Artisfera/MP3-Gotchi-v2/hardware/MP3-Gotchi-v2_kicad/MP3-Gotchi-v2_kicad.kicad_sch

## KiCad design hardware/MP3-Gotchi-v2_kicad/MP3-Gotchi-v2_kicad.kicad_sch (2026-07-09, an earlier design)

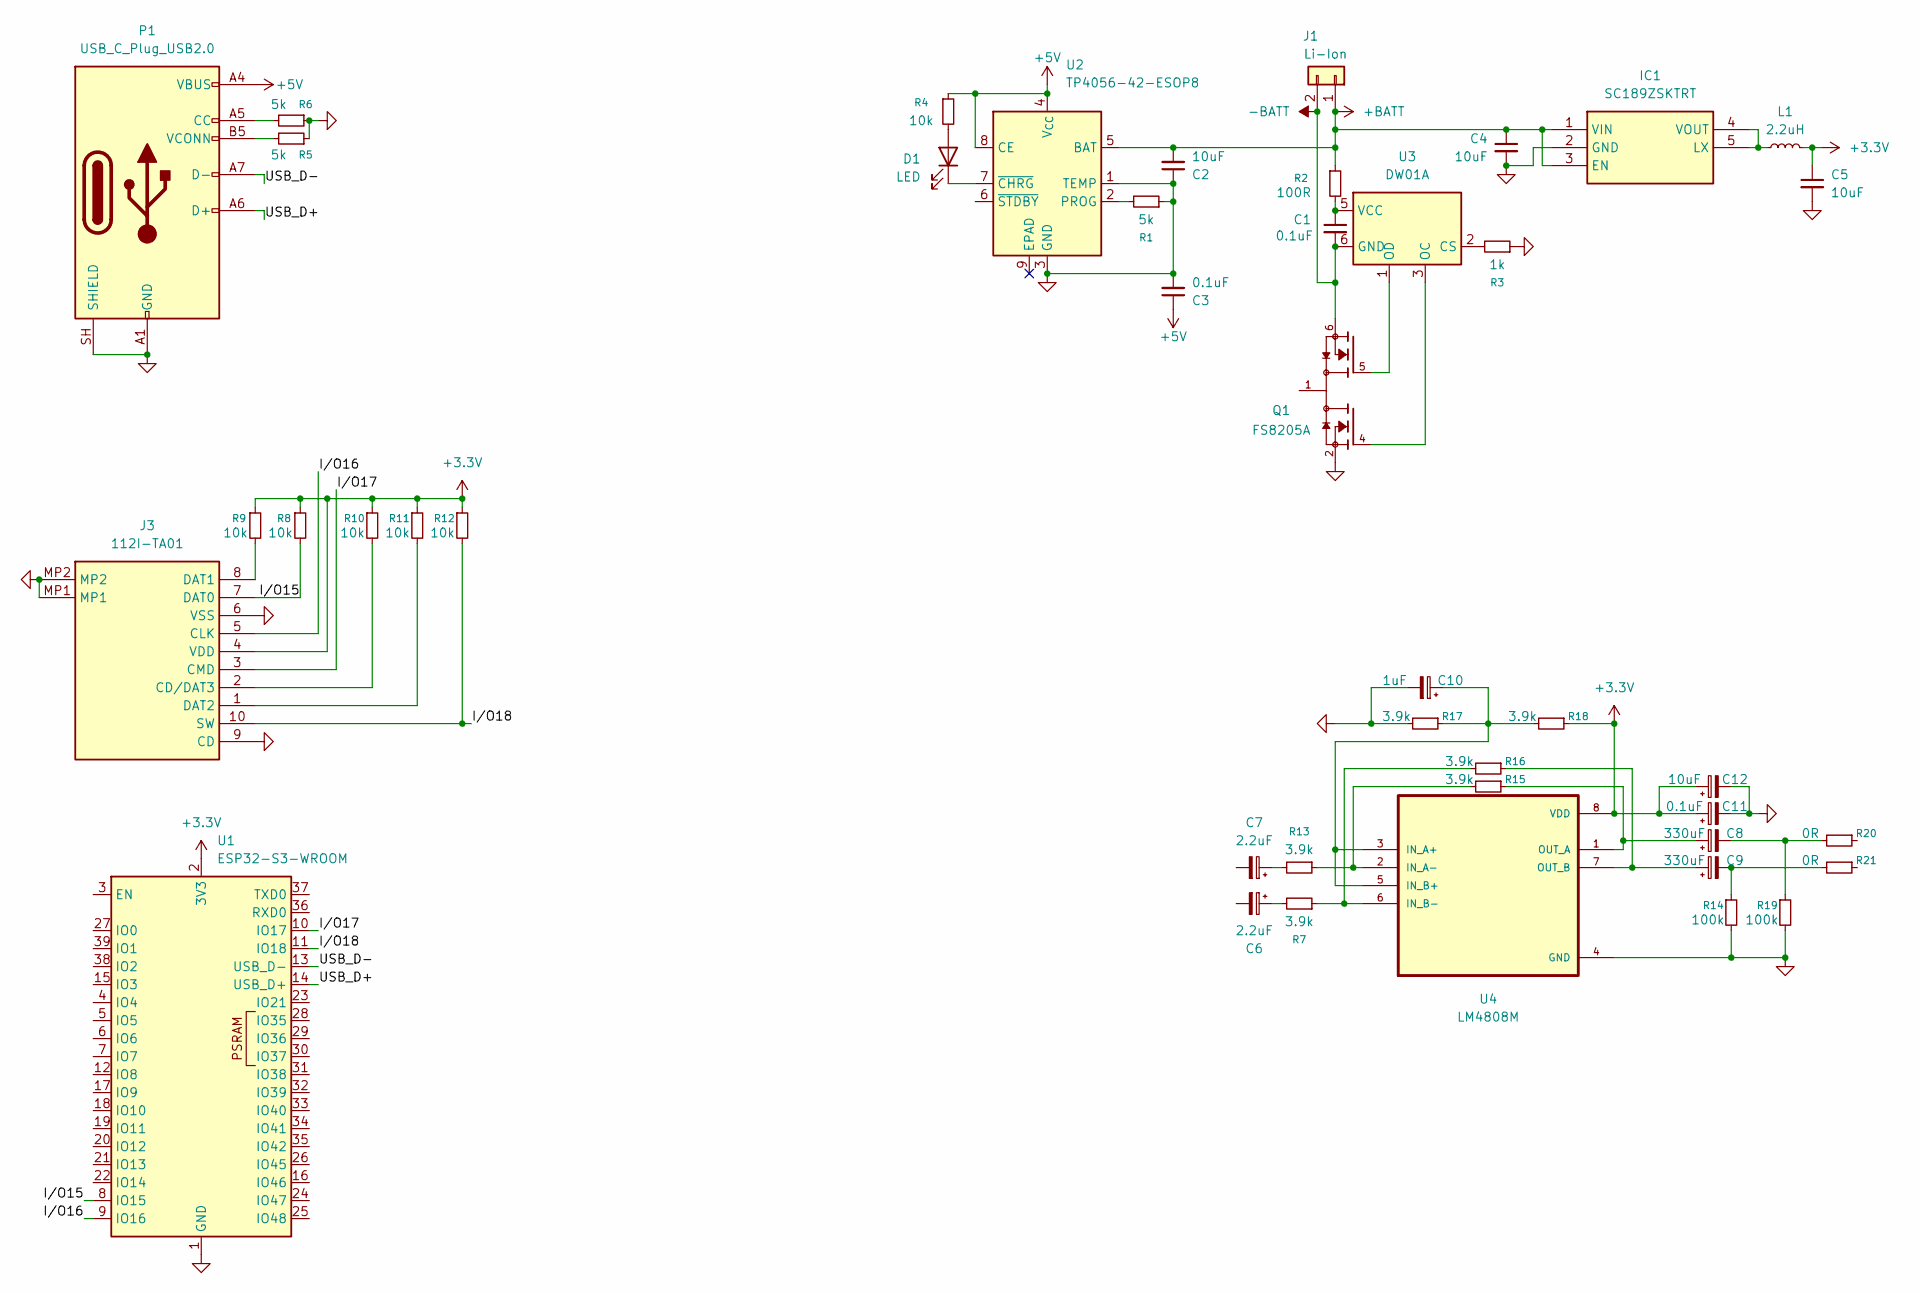
[picture p2: schematic MP3-Gotchi-v2_kicad.kicad_sch]

Parts:
C1, C3, C11: 0.1uF
C2, C4, C5, C12: 10uF
C6, C7: 2.2uF
C8, C9: 330uF
C10: 1uF
D1: LED
IC1: SC189ZSKTRT; SOT95P280X145-5N; Manufacturer_Part_Number SC189ZSKTRT
J1: Li-Ion
J3: 112I-TA01; 112ITA01; Manufacturer_Part_Number 112I-TA01
L1: 2.2uH
P1: USB_C_Plug_USB2.0
Q1: FS8205A; SOP65P640X120-8N; PARTREV 1.7
R1, R5, R6: 5k
R2: 100R
R3: 1k
R4, R8, R9, R10, R11, R12: 10k
R7, R13, R15, R16, R17, R18: 3.9k
R14, R19: 100k
R20, R21: 0R
U1: ESP32-S3-WROOM; ESP32-S3-WROOM-1
U2: TP4056-42-ESOP8; SOIC-8-1EP_3.9x4.9mm_P1.27mm_EP2.41x3.3mm_ThermalVias
U3: DW01A; SOT-23-6
U4: LM4808M; SOIC127P599X175-8N

Connections:
+3.3V: C5.1, C11.1, C12.1, J3.4 (VDD), L1.2, R8.1, R9.1, R10.1, R11.1, R12.1, R18.1, U1.2 (3V3), U4.8 (VDD)
+5V: C3.1, P1.A4 (VBUS), P1.A9 (VBUS), P1.B4 (VBUS), P1.B9 (VBUS), R4.1, U2.4 (V_{CC}), U2.8 (CE)
+BATT: C2.2, C4.1, IC1.1 (VIN), IC1.3 (EN), J1.1, R2.1, U2.5 (BAT)
-BATT: C1.2, J1.2, Q1.6, Q1.7, U3.6 (GND)
GND: C2.1, C3.2, C4.2, C5.2, C10.2, C11.2, C12.2, IC1.2 (GND), J3.6 (VSS), J3.9 (CD), J3.MP1, J3.MP2, P1.A1 (GND), P1.A12 (GND), P1.B1 (GND), P1.B12 (GND), P1.SH (SHIELD), Q1.2, Q1.3, R1.1, R3.1, R5.1, R6.1, R14.2, R17.2, R19.2, U1.1 (GND), U1.40 (GND), U1.41 (GND), U2.1 (TEMP), U2.3 (GND), U4.4 (GND)
I/O15: J3.7 (DAT0), R8.2, U1.8 (IO15)
I/O16: J3.5 (CLK), U1.9 (IO16)
I/O17: J3.3 (CMD), U1.10 (IO17)
I/O18: J3.10 (SW), R12.2, U1.11 (IO18)
unnamed: C1.1, R2.2, U3.5 (VCC)
unnamed: C6.1, R7.2
unnamed: C7.1, R13.2
unnamed: C8.1, R15.1, U4.1 (OUT_A)
unnamed: C8.2, R19.1, R20.2
unnamed: C9.1, R16.1, U4.7 (OUT_B)
unnamed: C9.2, R14.1, R21.2
unnamed: C10.1, R17.1, R18.2, U4.3 (IN_A+), U4.5 (IN_B+)
unnamed: D1.1 (K), U2.7 (~CHRG)
unnamed: D1.2 (A), R4.2
unnamed: IC1.4 (VOUT), IC1.5 (LX), L1.1
unnamed: J3.1 (DAT2), R11.2
unnamed: J3.2 (CD/DAT3), R10.2
unnamed: J3.8 (DAT1), R9.2
unnamed: P1.A5 (CC), R6.2
unnamed: P1.B5 (VCONN), R5.2
unnamed: Q1.1, Q1.8
unnamed: Q1.4, U3.3 (OC)
unnamed: Q1.5, U3.1 (OD)
unnamed: R1.2, U2.2 (PROG)
unnamed: R3.2, U3.2 (CS)
unnamed: R13.1, R15.2, U4.2 (IN_A-)
unnamed: R7.1, R16.2, U4.6 (IN_B-)
USB_D+: P1.A6 (D+), U1.14 (USB_D+)
USB_D-: P1.A7 (D-), U1.13 (USB_D-)
